noelvissers/nusynths-midictrl/src/Gui.cpp

#include "Gui.h"

#include <unordered_map>

#define OP_DECODEMODE 9
#define OP_INTENSITY 10
#define OP_SCANLIMIT 11
#define OP_SHUTDOWN 12
#define OP_DISPLAYTEST 15

CGui::CGui(int pinSs, int pinSck, int pinMosi)
{
  SPI_SS = pinSs;
  SPI_SCK = pinSck;
  SPI_MOSI = pinMosi;

  pinMode(SPI_SS, OUTPUT);
  pinMode(SPI_SCK, OUTPUT);
  pinMode(SPI_MOSI, OUTPUT);

  digitalWrite(SPI_SS, HIGH); // Disable device

  spiTransfer(OP_DISPLAYTEST, 0);
  spiTransfer(OP_SCANLIMIT, 3); // Show 4 digits
  spiTransfer(OP_DECODEMODE, 0);
  clear();
  shutdown(false);
  setBrightness(8); // Medium brightness
}

void CGui::startup()
{
  // Startup animation

  // LEDs
  clear();
  setLed(3, 0b10001000);
  delay(100);
  setLed(3, 0b00010001);
  delay(100);
  setLed(3, 0b00100010);
  delay(100);
  setLed(3, 0b01000100);
  delay(100);
  setLed(3, 0b00000000);

  // Snake
  setLed(0, 0b00000100);
  delay(75);
  setLed(0, 0b00000110);
  delay(75);
  setLed(0, 0b01000110);
  delay(75);
  setLed(0, 0b01000010);
  setLed(1, 0b01000000);
  delay(75);
  setLed(0, 0b01000000);
  setLed(2, 0b01000000);
  delay(75);
  setLed(0, 0b00000000);
  setLed(2, 0b01100000);
  delay(75);
  setLed(1, 0b00000000);
  setLed(2, 0b01101000);
  delay(75);
  setLed(2, 0b00101000);
  setLed(1, 0b00001000);
  delay(75);
  setLed(2, 0b00001000);
  setLed(0, 0b00001000);
  delay(75);
  setLed(2, 0b00000000);
  setLed(0, 0b00001100);
  delay(75);
  setLed(1, 0b00000000);
  setLed(0, 0b00001110);
  delay(75);

  // N
  setLed(0, 0b00000110);
  delay(75);
  setLed(0, 0b01000110);
  delay(75);
  setLed(0, 0b01100110);
  setLed(1, 0b00000010);
  delay(75);
  setLed(0, 0b01110110);
  setLed(1, 0b00000110);
  delay(75);

  // U
  setLed(1, 0b00001110);
  delay(75);
  setLed(1, 0b00011110);
  delay(75);
  setLed(1, 0b00111110);
}

void CGui::active()
{
  switch (mIdleState)
  {
  case 0:
    setLed(0, 0b00000001);
    setLed(1, 0b00000000);
    setLed(2, 0b00000000);
    mIdleState = 1;
    break;
  case 1:
    setLed(0, 0b00000000);
    setLed(1, 0b00000001);
    setLed(2, 0b00000000);
    mIdleState = 2;
    break;
  case 2:
    setLed(0, 0b00000000);
    setLed(1, 0b00000000);
    setLed(2, 0b00000001);
    mIdleState = 3;
    break;
  default:
    setLed(0, 0b00000000);
    setLed(1, 0b00000001);
    setLed(2, 0b00000000);
    mIdleState = 0;
    break;
  }
}

void CGui::setString(const std::string &str)
{
  static const std::unordered_map<char, byte> charMap = {
      {'0', 0b01111110},
      {'1', 0b00110000},
      {'2', 0b01101101},
      {'3', 0b01111001},
      {'4', 0b00110011},
      {'5', 0b01011011},
      {'6', 0b01011111},
      {'7', 0b01110000},
      {'8', 0b01111111},
      {'9', 0b01111011},
      {'A', 0b01110111},
      {'a', 0b01111101},
      {'B', 0b01111111},
      {'b', 0b00011111},
      {'C', 0b01001110},
      {'c', 0b00001101},
      {'D', 0b01111100},
      {'d', 0b00111101},
      {'E', 0b01001111},
      {'e', 0b01101111},
      {'F', 0b01000111},
      {'f', 0b01000111},
      {'G', 0b01011110},
      {'g', 0b01111011},
      {'H', 0b00110111},
      {'h', 0b00010111},
      {'I', 0b00110000},
      {'i', 0b00010000},
      {'J', 0b00111100},
      {'j', 0b00111000},
      {'K', 0b00101111},
      {'k', 0b01010111},
      {'L', 0b00001110},
      {'l', 0b00000110},
      {'M', 0b01010100},
      {'m', 0b00010100},
      {'N', 0b01110110},
      {'n', 0b00010101},
      {'O', 0b01111110},
      {'o', 0b00011101},
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

  unsigned int j = 0;
  for (unsigned int i = 0; i < str.size() && j < 3; i++)
  {
    char ch = str[i];

    if (ch == '.')
      continue;

    auto it = charMap.find(ch);
    uint16_t data = 0x00;
    if (it != charMap.end())
      data = it->second;

    if (i + 1 < str.size() && str[i + 1] == '.')
    {
      data |= 0x80; // Add dot
      i++;
    }

    setLed(j, data);
    j++;
  }

  // Clear remaining digits
  for (; j < 3; j++)
  {
    setLed(j, 0x00);
  }
}

void CGui::setOutputLed(uint8_t mask, bool state)
{
  if (state)
    mOutputLeds |= mask;
  else
    mOutputLeds &= ~mask;

  setLed(3, mOutputLeds);
}

void CGui::setLed(int digit, int value, bool dot)
{
  byte v = value;

  if (digit < 0 || digit > 7)
    return;
  if (dot)
    v |= 0x80;

  spiTransfer(digit + 1, v);
}

void CGui::setBrightness(int brightness)
{
  if (brightness >= 0 && brightness < 16)
    spiTransfer(OP_INTENSITY, brightness);
}

void CGui::shutdown(bool status)
{
  spiTransfer(OP_SHUTDOWN, !status);
}

void CGui::clear()
{
  for (int i = 0; i < 8; i++)
    spiTransfer(i + 1, 0);
  mIdleState = 0;
}

void CGui::setScanLimit(int limit)
{
  if (limit >= 0 && limit < 8)
    spiTransfer(OP_SCANLIMIT, limit);
}

void CGui::spiTransfer(volatile byte opcode, volatile byte data)
{
  if (!mActive)
    return;
  digitalWrite(SPI_SS, LOW);
  shiftOut(SPI_MOSI, SPI_SCK, MSBFIRST, opcode);
  shiftOut(SPI_MOSI, SPI_SCK, MSBFIRST, data);
  digitalWrite(SPI_SS, HIGH);
}
